justin-ham61/SmartBulbController/firmware/include/config.h

#ifndef CONFIG_H
#define CONFIG_H

typedef struct {
    const char* SSID;
    const char* PASSWORD;
} WifiParameters_t;

const char* SSID = "Odyssey 2.4GHz";
const char* PASS = "blue4524";
WifiParameters_t wifi_params = {SSID, PASS};

char* aliases[] = {
  "Lauter",
  "Dejsa",
  "Fado",
  "Strip"
};

extern int size;

#endif
